Jacajack/usynth/src/notes.c

#include "notes.h"

const uint16_t midi_notes[] PROGMEM =
{
	65536 * 8.176 / F_SAMPLE,
	65536 * 8.662 / F_SAMPLE,
	65536 * 9.177 / F_SAMPLE,
	65536 * 9.723 / F_SAMPLE,
	65536 * 10.301 / F_SAMPLE,
	65536 * 10.913 / F_SAMPLE,
	65536 * 11.562 / F_SAMPLE,
	65536 * 12.250 / F_SAMPLE,
	65536 * 12.978 / F_SAMPLE,
	65536 * 13.750 / F_SAMPLE,
	65536 * 14.568 / F_SAMPLE,
	65536 * 15.434 / F_SAMPLE,
	65536 * 16.352 / F_SAMPLE,
	65536 * 17.324 / F_SAMPLE,
	65536 * 18.354 / F_SAMPLE,
	65536 * 19.445 / F_SAMPLE,
	65536 * 20.602 / F_SAMPLE,
	65536 * 21.827 / F_SAMPLE,
	65536 * 23.125 / F_SAMPLE,
	65536 * 24.500 / F_SAMPLE,
	65536 * 25.957 / F_SAMPLE,
	65536 * 27.500 / F_SAMPLE,
	65536 * 29.135 / F_SAMPLE,
	65536 * 30.868 / F_SAMPLE,
	65536 * 32.703 / F_SAMPLE,
	65536 * 34.648 / F_SAMPLE,
	65536 * 36.708 / F_SAMPLE,
	65536 * 38.891 / F_SAMPLE,
	65536 * 41.203 / F_SAMPLE,
	65536 * 43.654 / F_SAMPLE,
	65536 * 46.249 / F_SAMPLE,
	65536 * 48.999 / F_SAMPLE,
	65536 * 51.913 / F_SAMPLE,
	65536 * 55.000 / F_SAMPLE,
	65536 * 58.270 / F_SAMPLE,
	65536 * 61.735 / F_SAMPLE,
	65536 * 65.406 / F_SAMPLE,
	65536 * 69.296 / F_SAMPLE,
	65536 * 73.416 / F_SAMPLE,
	65536 * 77.782 / F_SAMPLE,
	65536 * 82.407 / F_SAMPLE,
	65536 * 87.307 / F_SAMPLE,
	65536 * 92.499 / F_SAMPLE,
	65536 * 97.999 / F_SAMPLE,
	65536 * 103.826 / F_SAMPLE,
	65536 * 110.000 / F_SAMPLE,
	65536 * 116.541 / F_SAMPLE,
	65536 * 123.471 / F_SAMPLE,
	65536 * 130.813 / F_SAMPLE,
	65536 * 138.591 / F_SAMPLE,
	65536 * 146.832 / F_SAMPLE,
	65536 * 155.563 / F_SAMPLE,
	65536 * 164.814 / F_SAMPLE,
	65536 * 174.614 / F_SAMPLE,
	65536 * 184.997 / F_SAMPLE,
	65536 * 195.998 / F_SAMPLE,
	65536 * 207.652 / F_SAMPLE,
	65536 * 220.000 / F_SAMPLE,
	65536 * 233.082 / F_SAMPLE,
	65536 * 246.942 / F_SAMPLE,
	65536 * 261.626 / F_SAMPLE,
	65536 * 277.183 / F_SAMPLE,
	65536 * 293.665 / F_SAMPLE,
	65536 * 311.127 / F_SAMPLE,
	65536 * 329.628 / F_SAMPLE,
	65536 * 349.228 / F_SAMPLE,
	65536 * 369.994 / F_SAMPLE,
	65536 * 391.995 / F_SAMPLE,
	65536 * 415.305 / F_SAMPLE,
	65536 * 440.000 / F_SAMPLE,
	65536 * 466.164 / F_SAMPLE,
	65536 * 493.883 / F_SAMPLE,
	65536 * 523.251 / F_SAMPLE,
	65536 * 554.365 / F_SAMPLE,
	65536 * 587.330 / F_SAMPLE,
	65536 * 622.254 / F_SAMPLE,
	65536 * 659.255 / F_SAMPLE,
	65536 * 698.456 / F_SAMPLE,
	65536 * 739.989 / F_SAMPLE,
	65536 * 783.991 / F_SAMPLE,
	65536 * 830.609 / F_SAMPLE,
	65536 * 880.000 / F_SAMPLE,
	65536 * 932.328 / F_SAMPLE,
	65536 * 987.767 / F_SAMPLE,
	65536 * 1046.502 / F_SAMPLE,
	65536 * 1108.731 / F_SAMPLE,
	65536 * 1174.659 / F_SAMPLE,
	65536 * 1244.508 / F_SAMPLE,
	65536 * 1318.510 / F_SAMPLE,
	65536 * 1396.913 / F_SAMPLE,
	65536 * 1479.978 / F_SAMPLE,
	65536 * 1567.982 / F_SAMPLE,
	65536 * 1661.219 / F_SAMPLE,
	65536 * 1760.000 / F_SAMPLE,
	65536 * 1864.655 / F_SAMPLE,
	65536 * 1975.533 / F_SAMPLE,
	65536 * 2093.005 / F_SAMPLE,
	65536 * 2217.461 / F_SAMPLE,
	65536 * 2349.318 / F_SAMPLE,
	65536 * 2489.016 / F_SAMPLE,
	65536 * 2637.020 / F_SAMPLE,
	65536 * 2793.826 / F_SAMPLE,
	65536 * 2959.955 / F_SAMPLE,
	65536 * 3135.963 / F_SAMPLE,
	65536 * 3322.438 / F_SAMPLE,
	65536 * 3520.000 / F_SAMPLE,
	65536 * 3729.310 / F_SAMPLE,
	65536 * 3951.066 / F_SAMPLE,
	65536 * 4186.009 / F_SAMPLE,
	65536 * 4434.922 / F_SAMPLE,
	65536 * 4698.636 / F_SAMPLE,
	65536 * 4978.032 / F_SAMPLE,
	65536 * 5274.041 / F_SAMPLE,
	65536 * 5587.652 / F_SAMPLE,
	65536 * 5919.911 / F_SAMPLE,
	65536 * 6271.927 / F_SAMPLE,
	65536 * 6644.875 / F_SAMPLE,
	65536 * 7040.000 / F_SAMPLE,
	65536 * 7458.620 / F_SAMPLE,
	65536 * 7902.133 / F_SAMPLE,
	65536 * 8372.018 / F_SAMPLE,
	65536 * 8869.844 / F_SAMPLE,
	65536 * 9397.273 / F_SAMPLE,
	65536 * 9956.063 / F_SAMPLE,
	65536 * 10548.082 / F_SAMPLE,
	65536 * 11175.303 / F_SAMPLE,
	65536 * 11839.822 / F_SAMPLE,
};
